SensFanInFL/LaunchDisplay/STL/Front screws.jpg

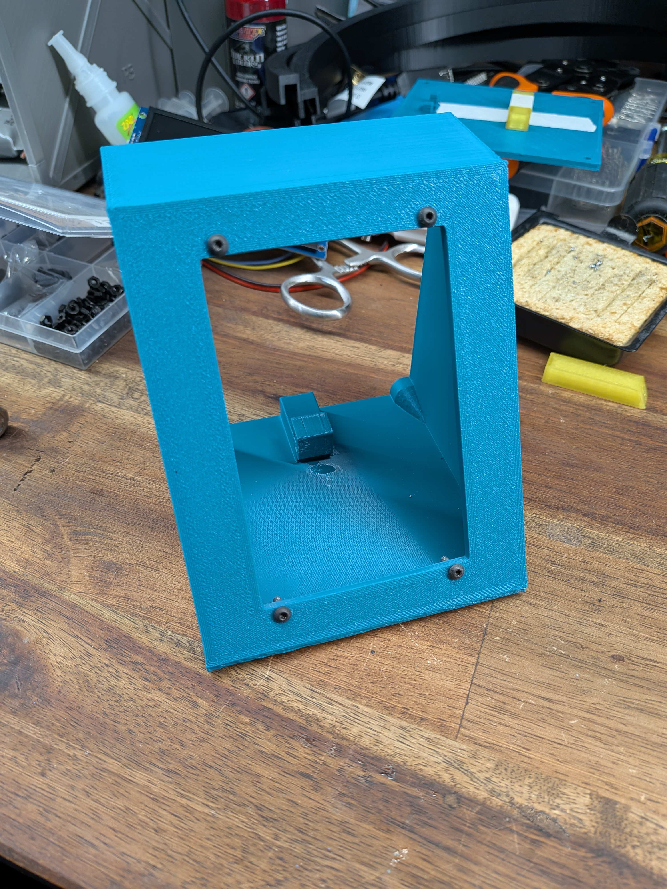
STL/Front screws.jpg
